ajokela/giga-shield/benchmark/pyplacer/giga_shield_v04_placed.png

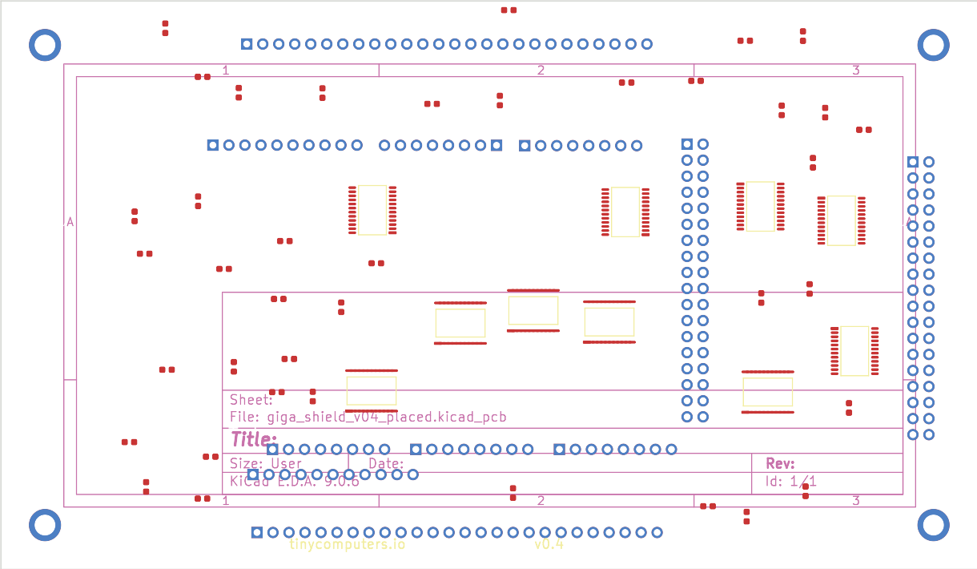
benchmark/pyplacer/giga_shield_v04_placed.png
