ajokela/giga-shield/benchmark/pyplacer/giga_shield_v04_routed_v2.png

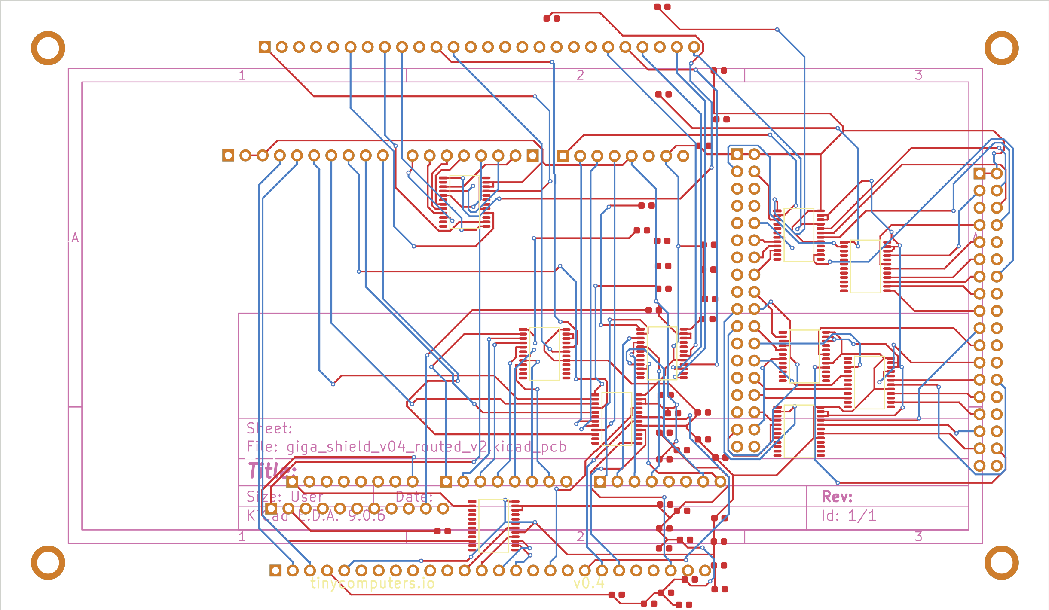
benchmark/pyplacer/giga_shield_v04_routed_v2.png
